Emmeline97/GoPro-Mount-for-Insect-Behavior/Docs/Images/IMG_0088.jpg

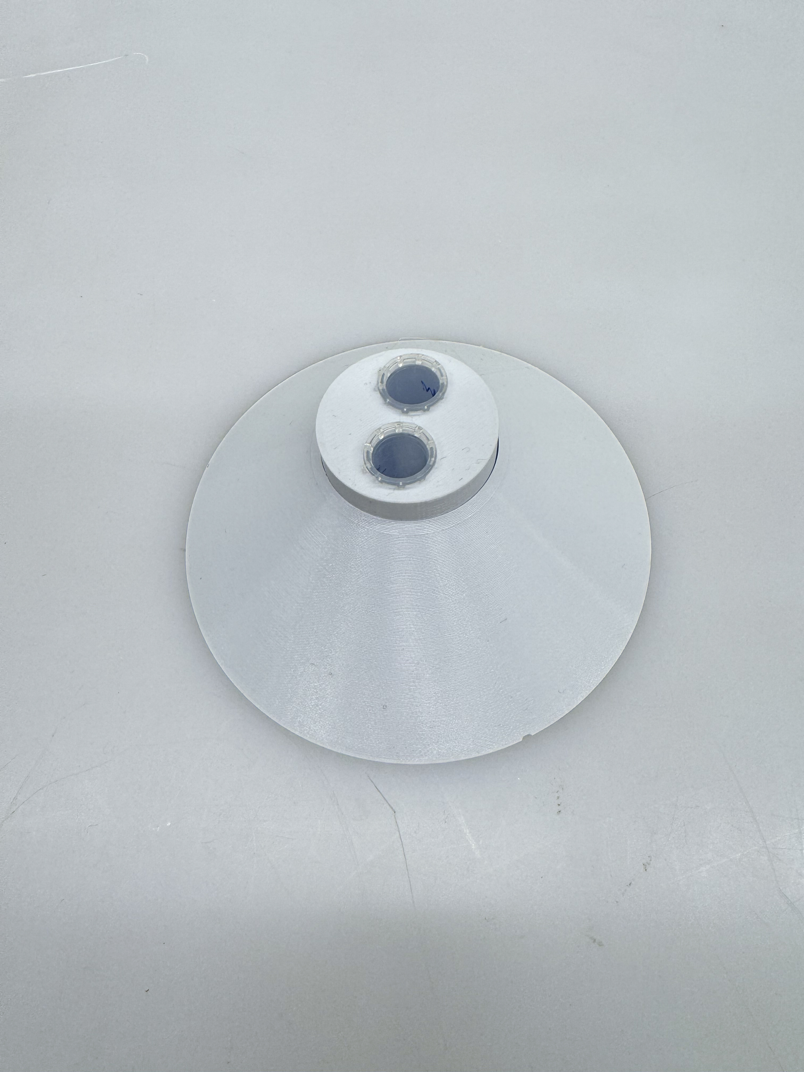
Docs/Images/IMG_0088.jpg
