Emmeline97/GoPro-Mount-for-Insect-Behavior/Docs/Images/IMG_0093.jpg

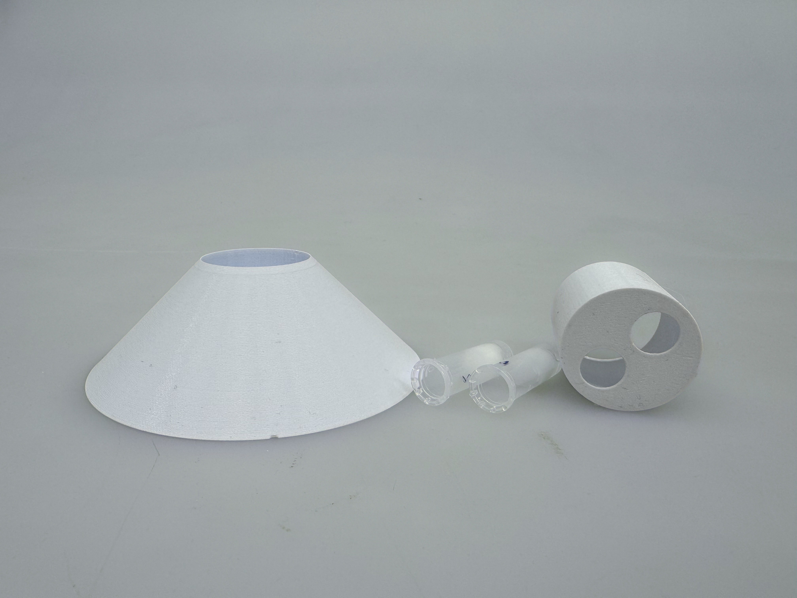
Docs/Images/IMG_0093.jpg
