Emmeline97/GoPro-Mount-for-Insect-Behavior/Docs/Images/IMG_0094.jpg

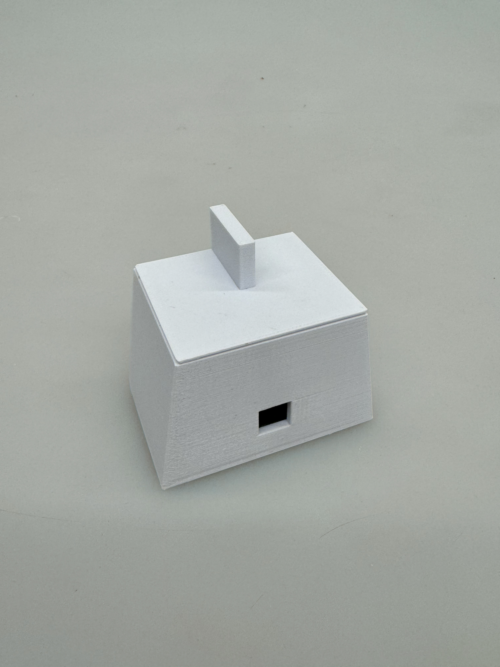
Docs/Images/IMG_0094.jpg
