Emmeline97/GoPro-Mount-for-Insect-Behavior/Docs/Images/IMG_0095.jpg

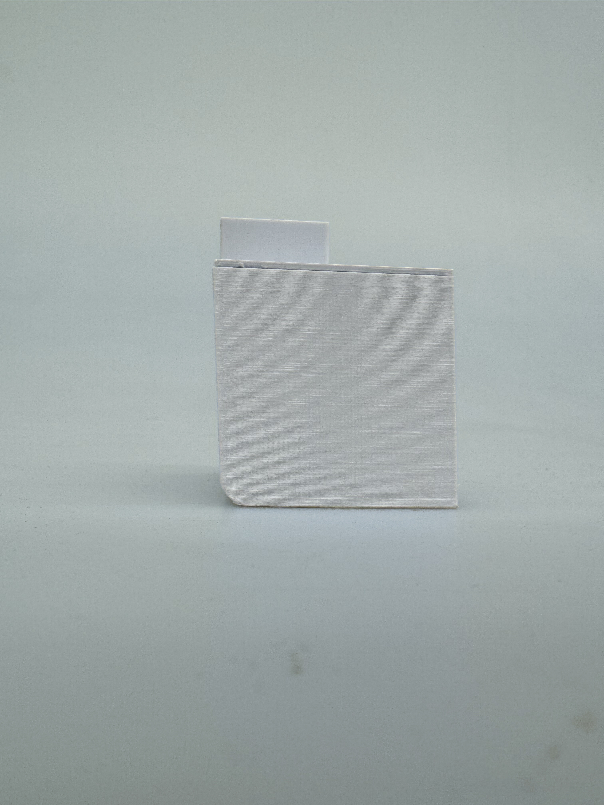
Docs/Images/IMG_0095.jpg
