Emmeline97/GoPro-Mount-for-Insect-Behavior/Docs/Images/IMG_0098.jpg

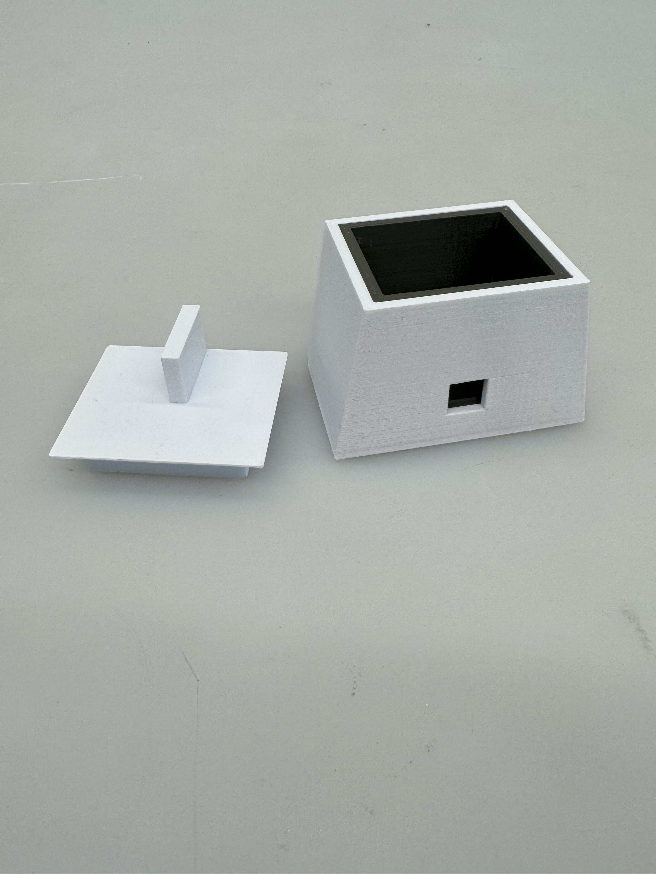
Docs/Images/IMG_0098.jpg
